pszopinski/whistle-back/Arduino/fft_buzzer/reversed128.h

#include <avr/pgmspace.h>


const int PROGMEM REVERSED[128] = {
  0,
  64,
  32,
  96,
  16,
  80,
  48,
  112,
  8,
  72,
  40,
  104,
  24,
  88,
  56,
  120,
  4,
  68,
  36,
  100,
  20,
  84,
  52,
  116,
  12,
  76,
  44,
  108,
  28,
  92,
  60,
  124,
  2,
  66,
  34,
  98,
  18,
  82,
  50,
  114,
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
};
